Fresita-codificadora/Mini_Whip_UNMDP/Amplificador_MiniWhip_Original_J310/amplificador.asc

C4: cap; 100n
C6: cap; 100n
C7: cap; 100n
J1: njf; J310
Q1: npn; 2N3866
R3: res; 10k
R4: res; 56
R5: res; 2.7k
R9: res; 220
R14: res; 680
R15: res; 1Meg
R16: res; 1Meg
R17: res; 1Meg
V2: voltage; ""; AC 1
V4: voltage; 12
V7: voltage; 0
Named nets: 0, vi
.MODEL J310 NJF(VTO=-3.8366 BETA=2.88371m BETATCE=-0.5 LAMBDA=2.00998E-2 RD=1.53610 RS=1.53610 CGS=7.40000p CGD=6.20000p PB=7.58274E-1 IS=4.18900E-16 XTI=3 AF=1 FC=0.5 N=1 NR=2 MFG=PHILIPS)
.MODEL 2N5109 NPN ( BF=44 VAF=160 VAR=16 RC=0.69 RB=1.57 RE=2.75 IKF=0.28 ISE=0.36E-13 TF=0.111n TR=8n ITF=0.82E-01 VTF=0.66E+01 CJC=3p CJE=2p XTI=3.0 NE=1.5 ISC=0.12E-13 EG=1.11 XTB=1.5 BR=1.14 VJC=0.75 VJE=0.75 IS=0.40E-14 MJC=0.33 MJE=0.33 XTF=4 IKR=0.28 KF=1f NC=1.7 FC=0.5 RBM=1.1 IRB=0.40E-01 XCJC=0.5 mfg=Motorola )
.ac dec 100 100 1000meg
.MODEL 2N3866  NPN (
+ IS=13.232E-12
+ BF=1.2948E3
+ VAF=100
+ IKF=.13116
+ ISE=785.43E-12
+ NE=1.7362
+ BR=1.0408
+ VAR=100
+ IKR=3.3880
+ ISC=13.232E-12
+ NC=1.4860
+ NK=.72187
+ RB=8.9057
+ RC=1.7862
+ CJE=31.375E-12
+ VJE=.87558
+ MJE=.31831
+ CJC=7.3111E-12
+ VJC=.76419
+ MJC=.30725
+ TF=178.96E-12
+ XTF=10.044
+ VTF=10.275
+ ITF=5.8742
+ TR=10.000E-9 )
