Fresita-codificadora/Mini_Whip_UNMDP/Amplificador_MiniWhip_segunda_opcion/amplificador segunda opcion.asc

C1: cap; 33.4p
J1: njf; 2N4416
Q1: npn; 2N3904
R1: res; 2.2Meg
R2: res; 10Meg
R3: res; 1Meg
R4: res; 10k
R5: res; 10k
R6: res; 1k
R7: res; 10
V1: voltage; ""; AC 1
V2: voltage; 30
V3: voltage; 0
Named nets: 0
.ac dec 100 .1 100meg
