Fresita-codificadora/Mini_Whip_UNMDP/Amplificador_MiniWhip_Tercera_opcion/amplificador segunda opcion.asc

C1: cap; 33.4p
C2: cap; 100µ
J1: njf; J112
Q1: npn; 2N2222
R1: res; 2.2Meg
R2: res; 10Meg
R3: res; 1Meg
R4: res; 10k
R5: res; 10k
R6: res; 1k
R7: res; 10
R8: res; 100k
V1: voltage; SINE(0 .11 100k); AC 1
V2: voltage; 12
V3: voltage; 0
Named nets: 0
.ac dec 100 .1 100meg
.tran .1
