Fresita-codificadora/Mini_Whip_UNMDP/MiniWhip_con_2N7000/mosfet 2N7000.asc

C1: cap; 100n
C2: cap; 100n
C3: cap; 100n
M1: nmos; 2N7002
Q1: npn; 2N2222
R1: res; 680
R2: res; 1Meg
R3: res; 1Meg
R4: res; 330k
R5: res; 2700
R6: res; 4700
R7: res; 470
R8: res; 47
R9: res; 1
V1: voltage; 15
V2: voltage; ""; AC 1
V4: voltage; 15
Named nets: 0
.op
.ac dec 100 100 1G
.tran .1
